softegg/Stylish-Trucker-Belt-Synthesizer/photos/Back of v4 plastic enclosure.JPG

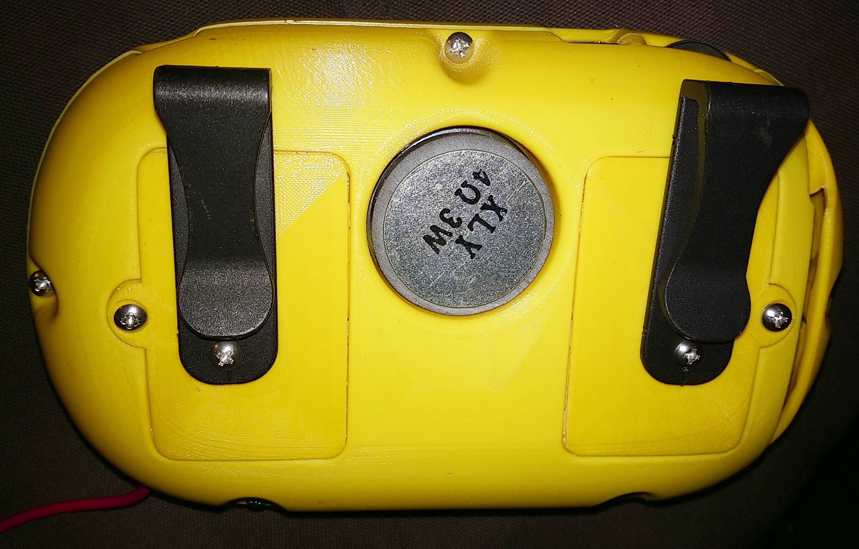
photos/Back of v4 plastic enclosure.JPG
