softegg/Stylish-Trucker-Belt-Synthesizer/photos/PCBs from Ai Green 2.jpg

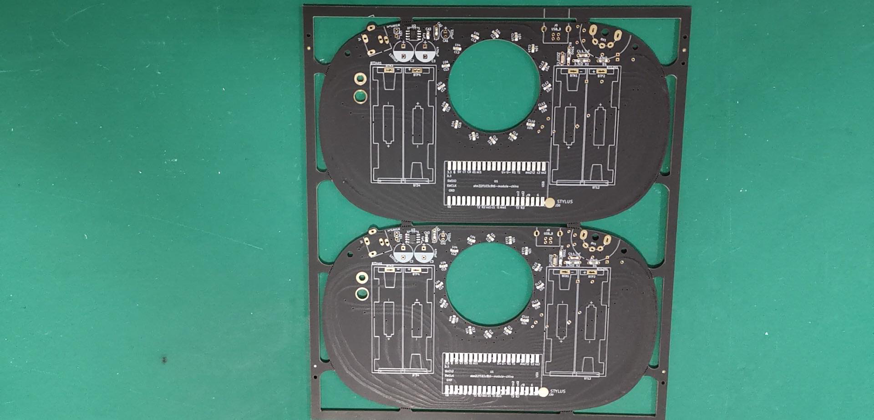
photos/PCBs from Ai Green 2.jpg
