softegg/Stylish-Trucker-Belt-Synthesizer/renders etc/board back only.png

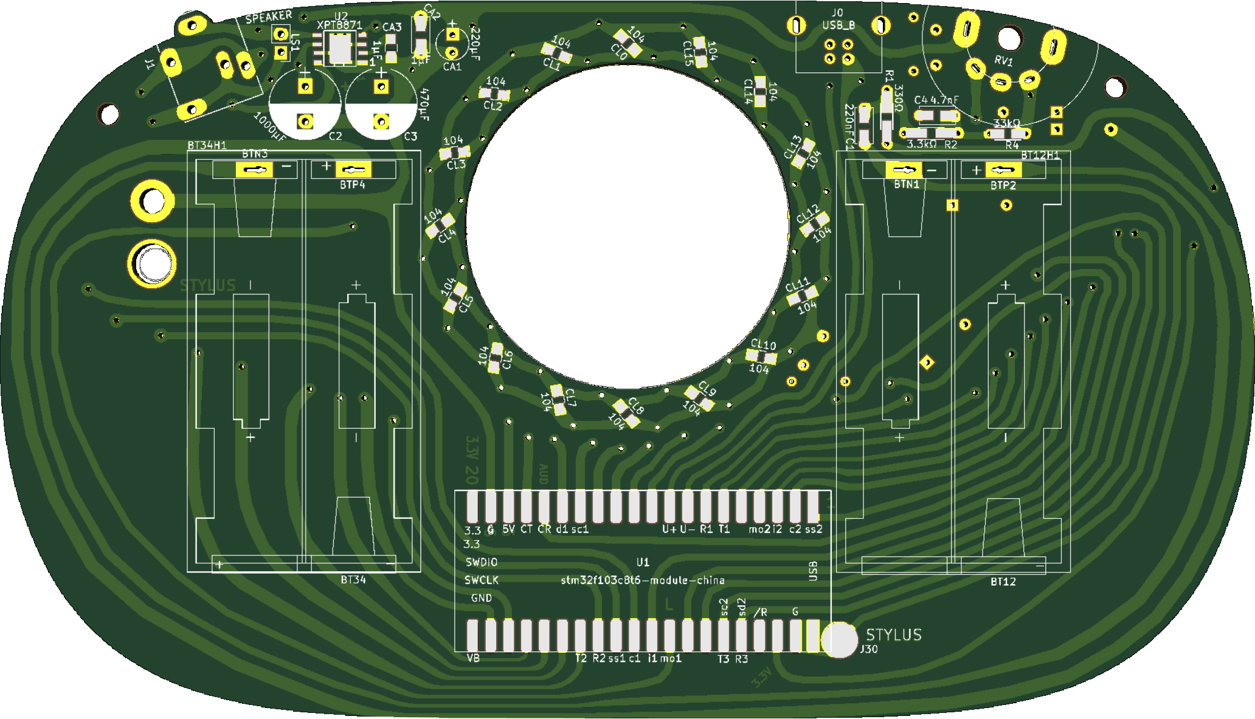
renders etc/board back only.png
