softegg/Stylish-Trucker-Belt-Synthesizer/renders etc/board front only.png

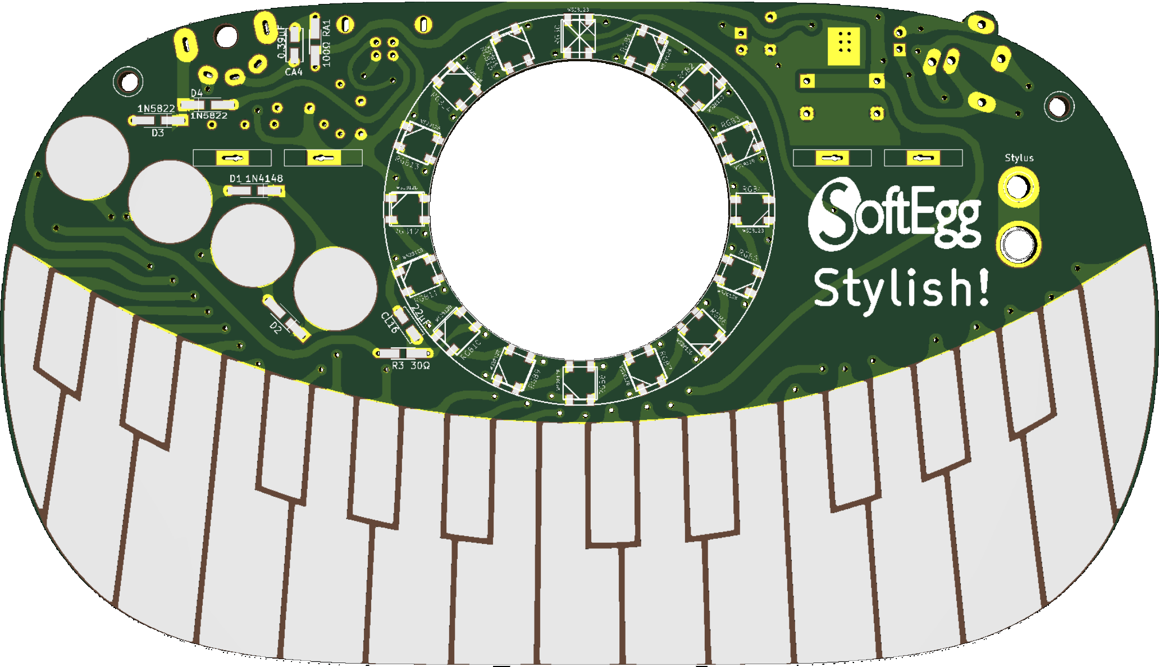
renders etc/board front only.png
