softegg/Stylish-Trucker-Belt-Synthesizer/renders etc/Stylish PCB V4.PNG

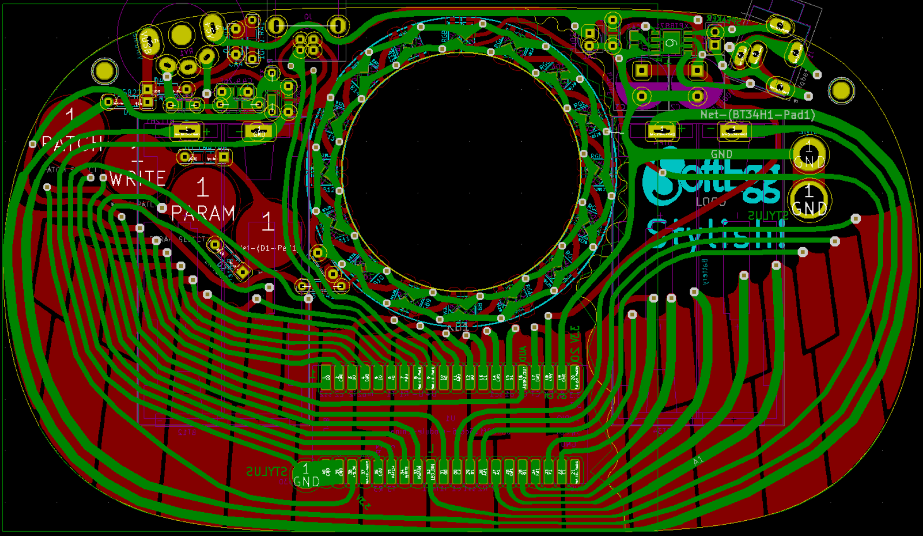
renders etc/Stylish PCB V4.PNG
