softegg/Stylish-Trucker-Belt-Synthesizer/3d models/Normal Models/STEP/Stylish Belt Synth V4 LED Bezel.step

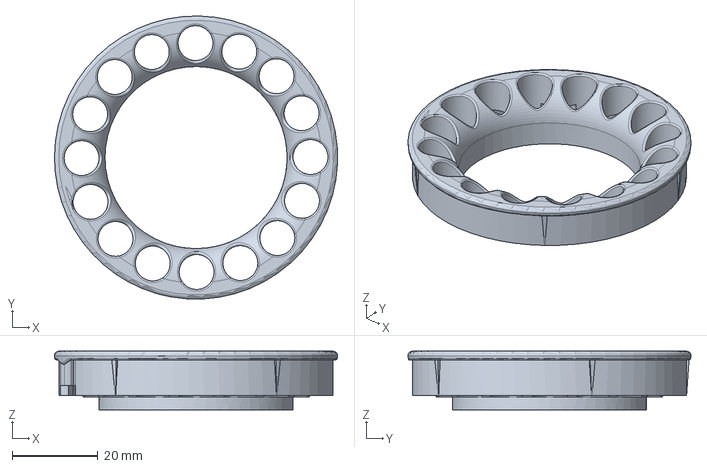
[picture p25: CAD file, 2019-10-15]
3d models/Normal Models/STEP/Stylish Belt Synth V4 LED Bezel.step
65.8 x 65.8 x 13.6 mm
