softegg/Stylish-Trucker-Belt-Synthesizer/3d models/Stylish Belt Synth V2 Left Battery Door.step

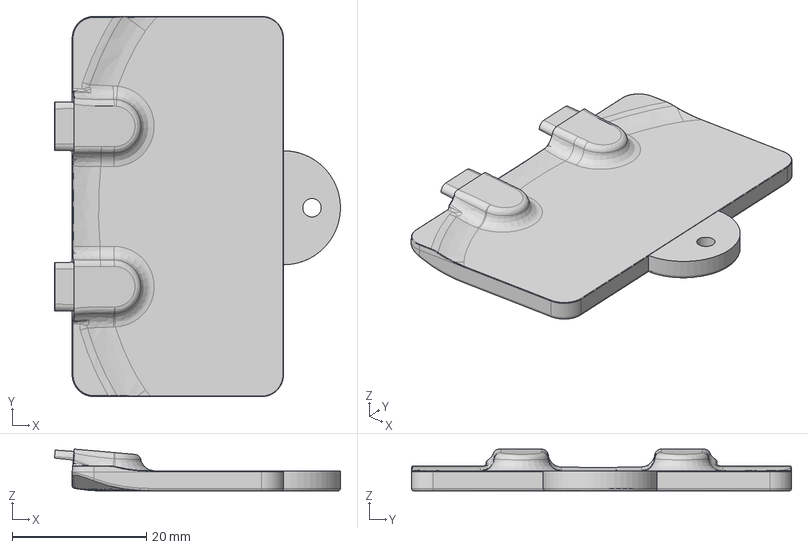
[picture p26: CAD file, 2019-07-12]
3d models/Stylish Belt Synth V2 Left Battery Door.step
42.6 x 56.7 x 6.25 mm
