softegg/Stylish-Trucker-Belt-Synthesizer/3d models/woodCNC/StylishWoodFrontFixtureCNC.stl

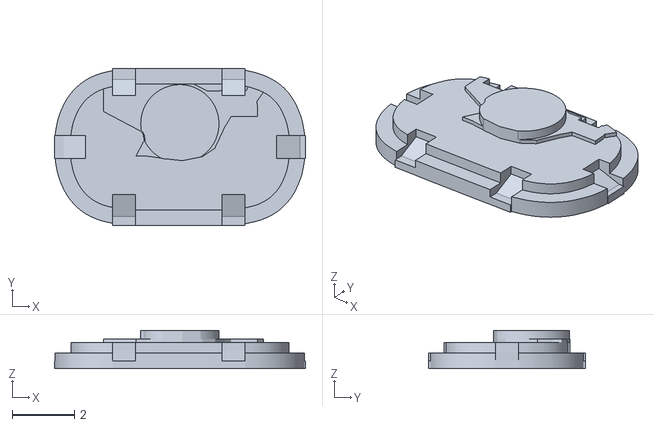
[picture p27: CAD file, 2019-08-12]
3d models/woodCNC/StylishWoodFrontFixtureCNC.stl
8.06 x 5.06 x 1.22
