softegg/Stylish-Trucker-Belt-Synthesizer/3d models/Mold/Negative/STEP/Stylish Belt Synth - Top - Outside Negative.step

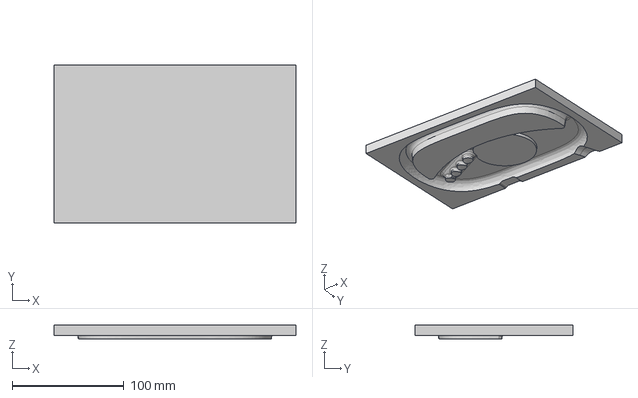
[picture p28: CAD file, 2020-02-13]
3d models/Mold/Negative/STEP/Stylish Belt Synth - Top - Outside Negative.step
216.3 x 141.5 x 12.6 mm
