softegg/Stylish-Trucker-Belt-Synthesizer/3d models/Mold/Positive - Mold Molds/STEP/Stylish Belt Synth - LED Lightpipe- Inside Positive.step

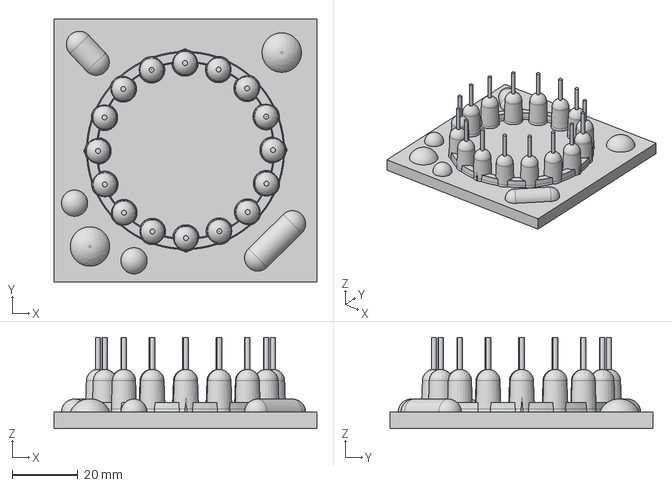
[picture p29: CAD file, 2020-03-12]
3d models/Mold/Positive - Mold Molds/STEP/Stylish Belt Synth - LED Lightpipe- Inside Positive.step
80.0 x 80.0 x 27.8 mm
LED Bezel
LED Lightpipe
