softegg/Stylish-Trucker-Belt-Synthesizer/3d models/Stylish Belt Synth V2 Switch Toggle.step

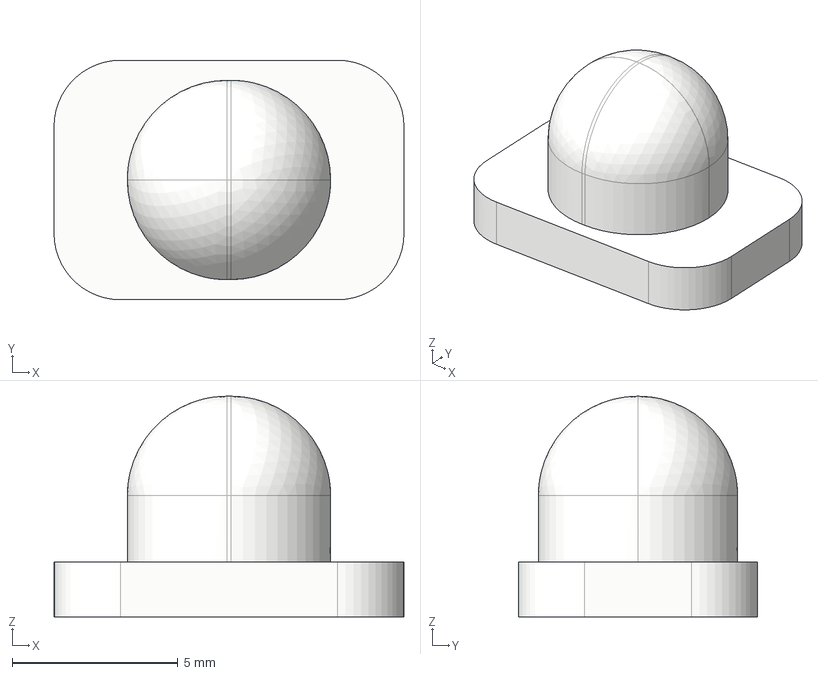
[picture p30: CAD file, 2019-07-12]
3d models/Stylish Belt Synth V2 Switch Toggle.step
10.5 x 7.22 x 6.65 mm
