softegg/Stylish-Trucker-Belt-Synthesizer/3d models/woodCNC/StylishWoodBackFixtureCNC.stl

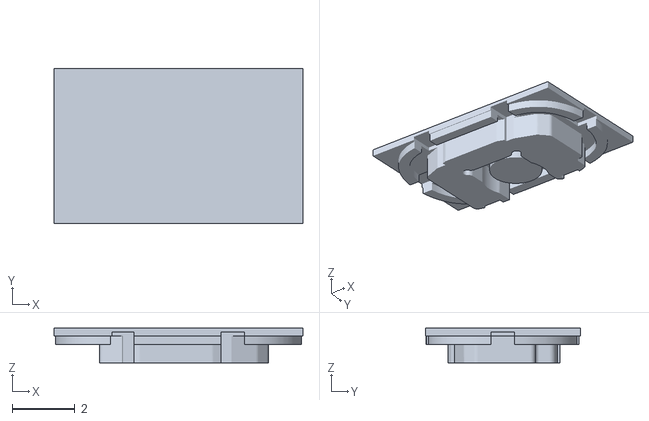
[picture p31: CAD file, 2019-08-12]
3d models/woodCNC/StylishWoodBackFixtureCNC.stl
7.92 x 4.94 x 1.11
