softegg/Stylish-Trucker-Belt-Synthesizer/3d models/Mold/Positive - Mold Molds/STEP/Stylish Belt Synth - LED Bezel - Outside Positive.step

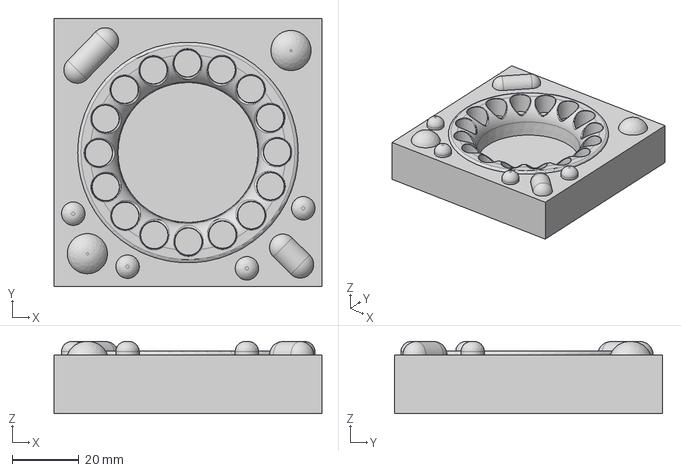
[picture p33: CAD file, 2020-03-12]
3d models/Mold/Positive - Mold Molds/STEP/Stylish Belt Synth - LED Bezel - Outside Positive.step
80.0 x 80.0 x 21.5 mm
