softegg/Stylish-Trucker-Belt-Synthesizer/3d models/Stylish Belt Synth V2 Bezel.stl

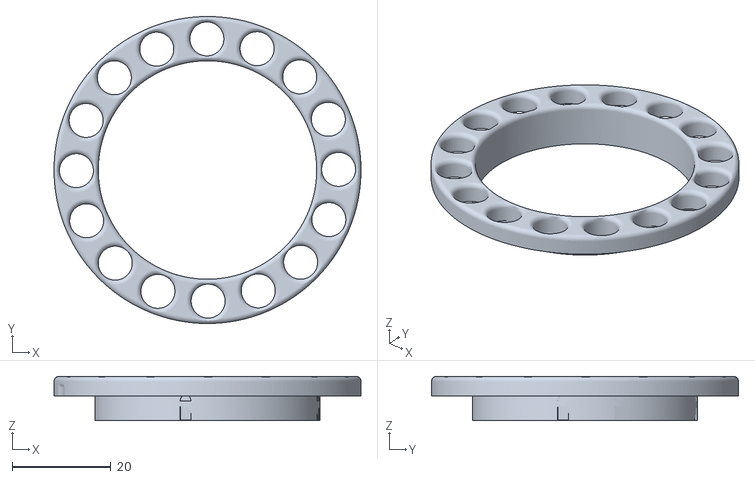
[picture p34: CAD file, 2019-06-09]
3d models/Stylish Belt Synth V2 Bezel.stl
62.3 x 62.3 x 9.00
