softegg/Stylish-Trucker-Belt-Synthesizer/3d models/woodCNC/StylishWoodFrontCNC.stl

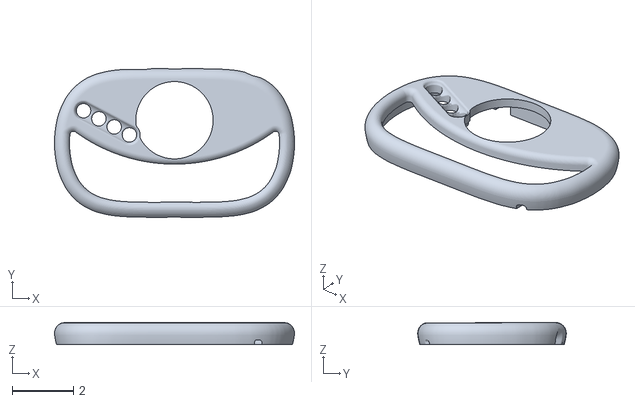
[picture p35: CAD file, 2019-08-07]
3d models/woodCNC/StylishWoodFrontCNC.stl
7.87 x 4.87 x 0.726
