softegg/Stylish-Trucker-Belt-Synthesizer/3d models/Mold/Negative/STEP/Stylish Belt Synth - Battery Door 2 - Inside Negative.step

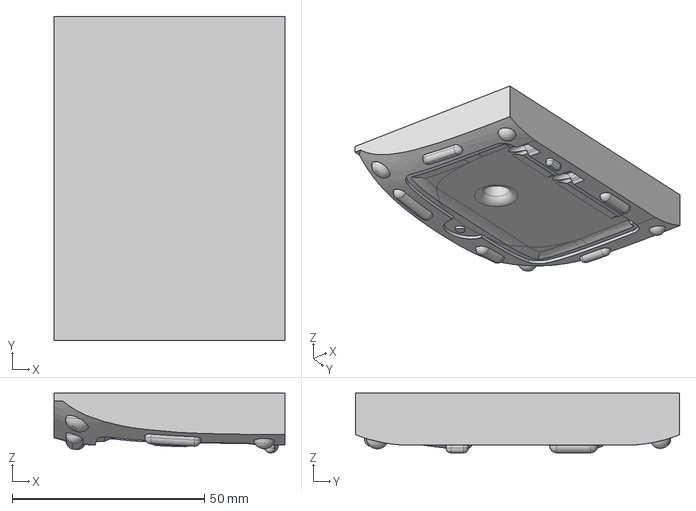
[picture p36: CAD file, 2020-01-29]
3d models/Mold/Negative/STEP/Stylish Belt Synth - Battery Door 2 - Inside Negative.step
60.0 x 84.3 x 15.5 mm
