softegg/Stylish-Trucker-Belt-Synthesizer/3d models/Belt Clip.stl

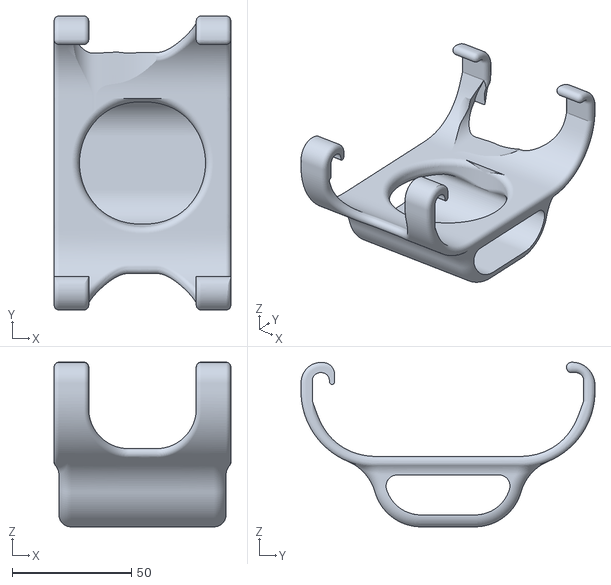
[picture p37: CAD file, 2018-11-03]
3d models/Belt Clip.stl
74.0 x 123.1 x 68.9
