softegg/Stylish-Trucker-Belt-Synthesizer/3d models/Mold/Negative/STEP/Stylish Belt Synth - Battery Door 1 - Outside Negative.step

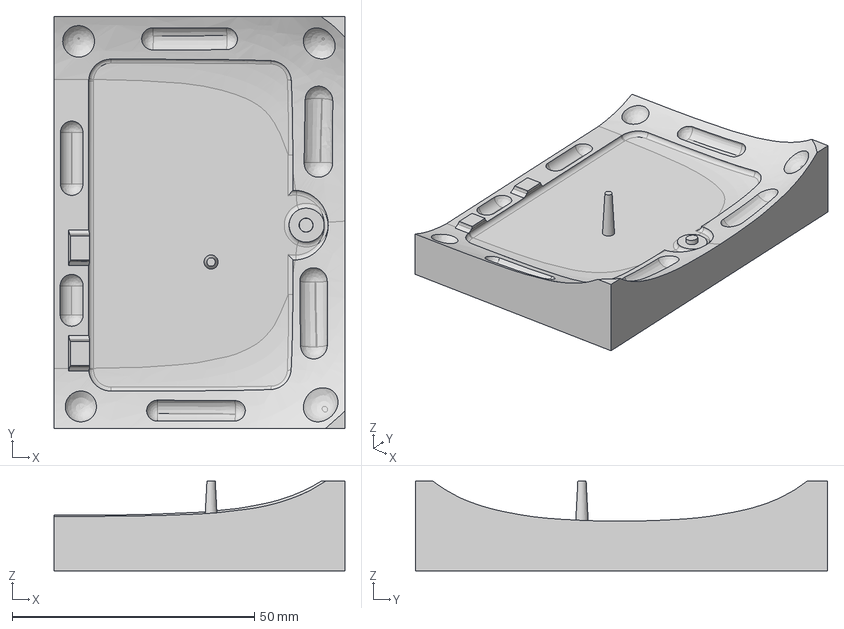
[picture p38: CAD file, 2020-01-29]
3d models/Mold/Negative/STEP/Stylish Belt Synth - Battery Door 1 - Outside Negative.step
60.0 x 85.0 x 18.5 mm
