softegg/Stylish-Trucker-Belt-Synthesizer/3d models/Mold/Positive - Mold Molds/STEP/Stylish Belt Synth - Battery Door 1 - Inside Positive.step

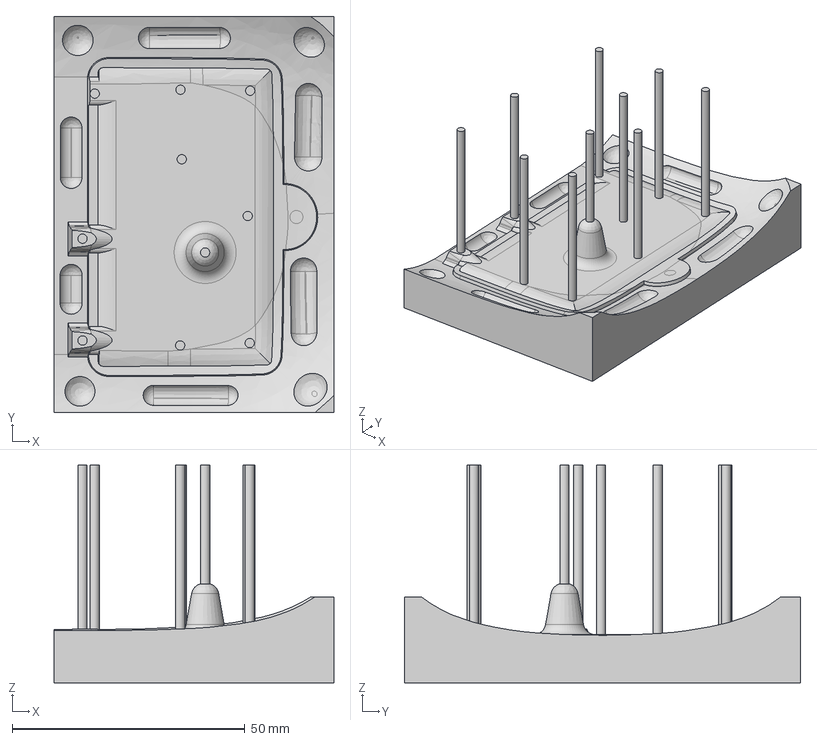
[picture p39: CAD file, 2020-01-29]
3d models/Mold/Positive - Mold Molds/STEP/Stylish Belt Synth - Battery Door 1 - Inside Positive.step
60.0 x 85.0 x 46.8 mm
