softegg/Stylish-Trucker-Belt-Synthesizer/3d models/woodCNC/Stylish Belt Synth CNC Wood Top Interior.dxf

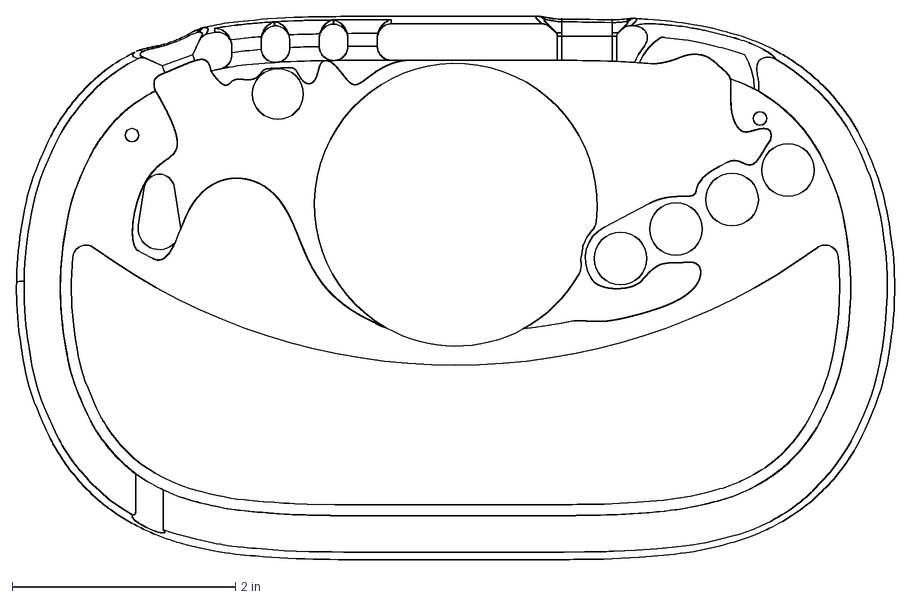
[picture p40: CAD file, 2019-08-07]
3d models/woodCNC/Stylish Belt Synth CNC Wood Top Interior.dxf
7.87 x 4.87 in
