softegg/Stylish-Trucker-Belt-Synthesizer/3d models/LED Bezel Outer Black TPE.stl

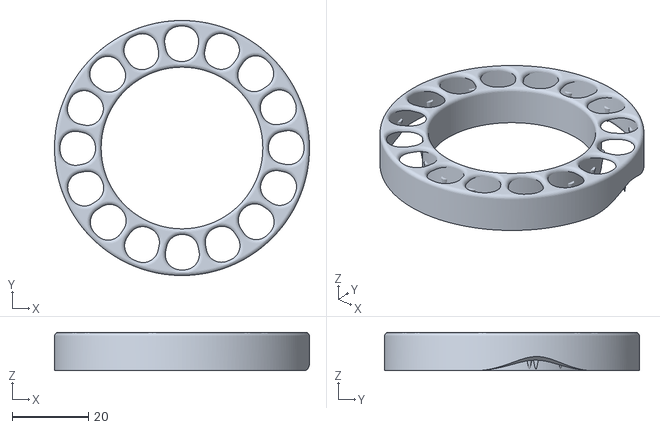
[picture p41: CAD file, 2018-11-03]
3d models/LED Bezel Outer Black TPE.stl
66.8 x 66.8 x 10.1
