softegg/Stylish-Trucker-Belt-Synthesizer/3d models/Mold/Negative/STEP/Stylish Belt Synth - Battery Door 2 - Outside Negative.step

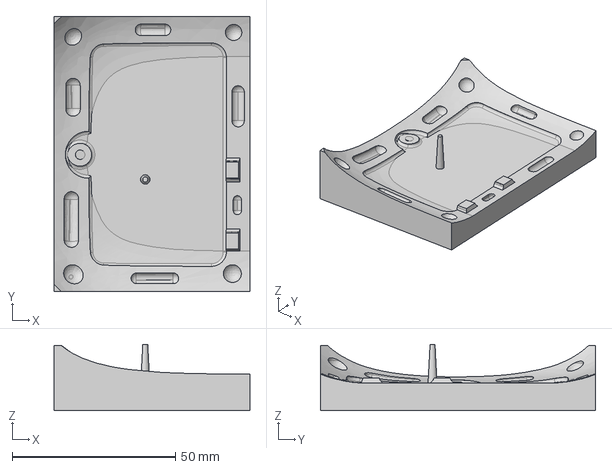
[picture p42: CAD file, 2020-01-29]
3d models/Mold/Negative/STEP/Stylish Belt Synth - Battery Door 2 - Outside Negative.step
60.0 x 84.3 x 20.4 mm
