softegg/Stylish-Trucker-Belt-Synthesizer/3d models/woodCNC/Stylish Belt Synth CNC Wood Bottom Interior.dxf

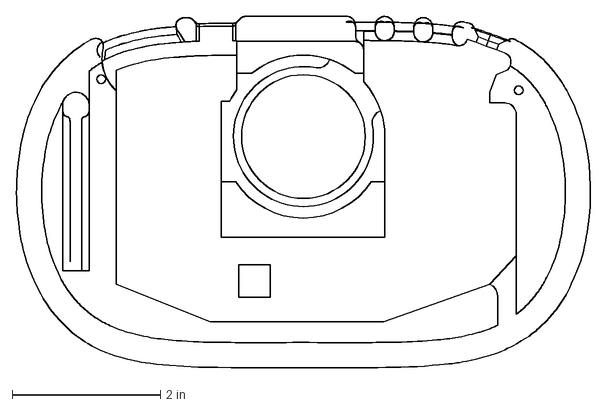
[picture p43: CAD file, 2019-08-04]
3d models/woodCNC/Stylish Belt Synth CNC Wood Bottom Interior.dxf
7.74 x 4.73 in
