softegg/Stylish-Trucker-Belt-Synthesizer/3d models/Amp Cover.stl

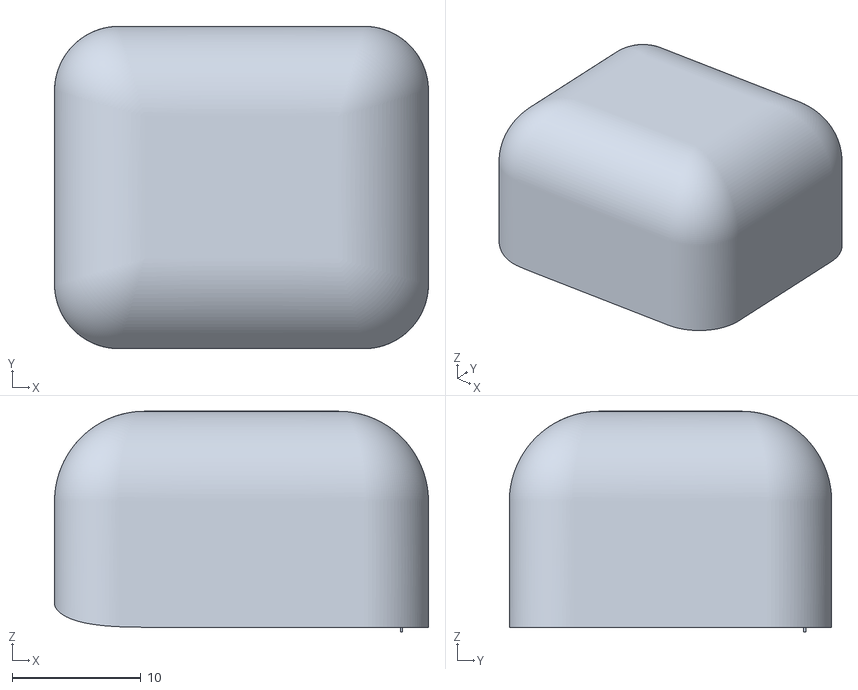
[picture p44: CAD file, 2018-11-03]
3d models/Amp Cover.stl
29.0 x 25.0 x 17.1
