softegg/Stylish-Trucker-Belt-Synthesizer/3d models/Mold/Negative/STEP/Stylish Belt Synth - Bottom - Outside Negative.step

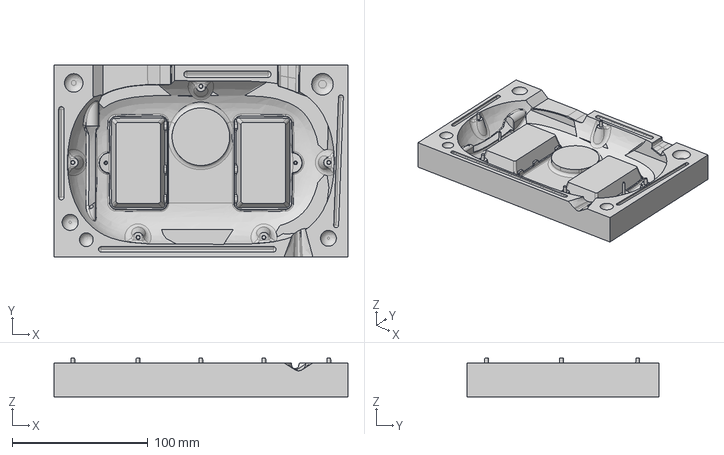
[picture p45: CAD file, 2020-01-27]
3d models/Mold/Negative/STEP/Stylish Belt Synth - Bottom - Outside Negative.step
216.3 x 141.5 x 28.5 mm
Top top
Bottom Molds
