softegg/Stylish-Trucker-Belt-Synthesizer/3d models/Mold/Positive - Mold Molds/STEP/Stylish Belt Synth - Battery Door 2 - Inside Positive.step

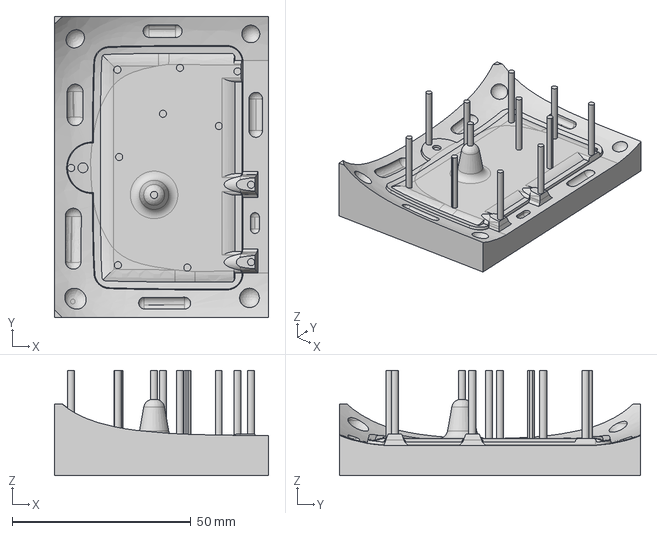
[picture p46: CAD file, 2020-01-29]
3d models/Mold/Positive - Mold Molds/STEP/Stylish Belt Synth - Battery Door 2 - Inside Positive.step
60.0 x 84.3 x 29.4 mm
