softegg/Stylish-Trucker-Belt-Synthesizer/3d models/woodCNC/Stylish Belt Synth CNC Wood Top Fixturing Jig.dxf

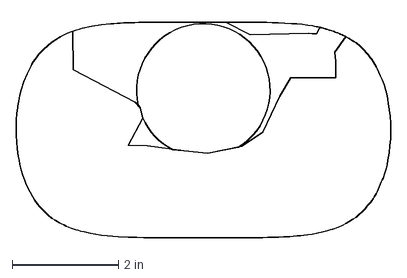
[picture p47: CAD file, 2019-08-01]
3d models/woodCNC/Stylish Belt Synth CNC Wood Top Fixturing Jig.dxf
7.06 x 4.18 in
