softegg/Stylish-Trucker-Belt-Synthesizer/3d models/Front v2.stl

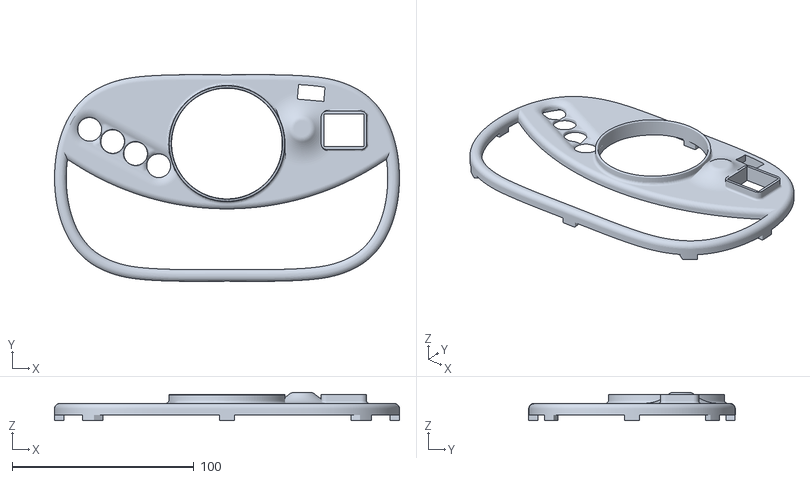
[picture p48: CAD file, 2018-11-03]
3d models/Front v2.stl
189.8 x 113.7 x 15.5
