softegg/Stylish-Trucker-Belt-Synthesizer/3d models/Mold/Positive - Mold Molds/STEP/Stylish Belt Synth - Bottom - Outside Positive.step

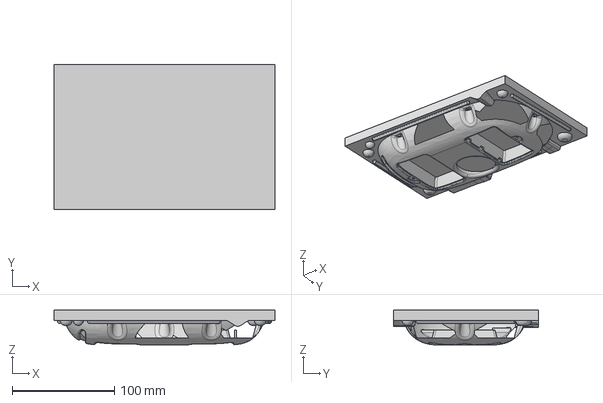
[picture p49: CAD file, 2020-01-27]
3d models/Mold/Positive - Mold Molds/STEP/Stylish Belt Synth - Bottom - Outside Positive.step
216.3 x 141.5 x 34.0 mm
Top top
Bottom Molds
