softegg/Stylish-Trucker-Belt-Synthesizer/3d models/woodCNC/Stylish Belt Synth CNC Wood Bottom Fixturing Jig.dxf

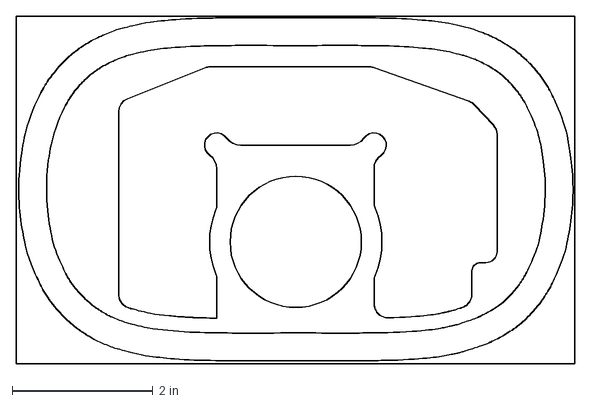
[picture p50: CAD file, 2019-07-18]
3d models/woodCNC/Stylish Belt Synth CNC Wood Bottom Fixturing Jig.dxf
7.92 x 4.94 in
