softegg/Stylish-Trucker-Belt-Synthesizer/3d models/LED Bezel Inner Translucent PLA.stl

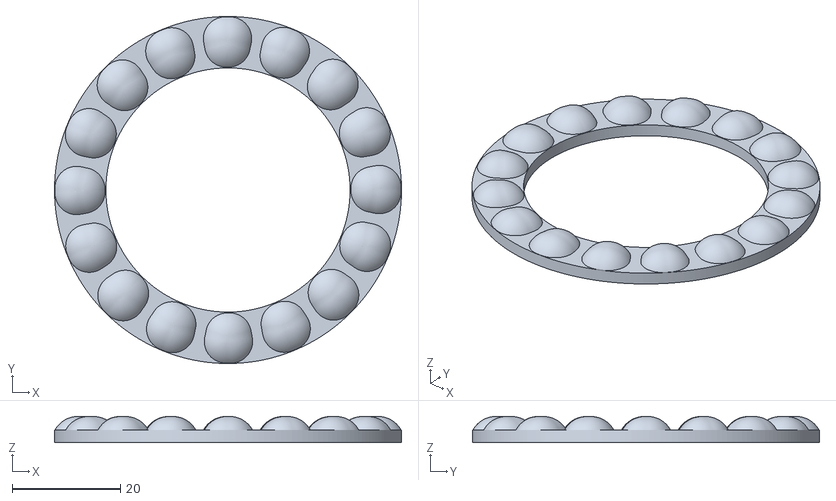
[picture p51: CAD file, 2018-11-03]
3d models/LED Bezel Inner Translucent PLA.stl
64.0 x 64.0 x 4.80
