softegg/Stylish-Trucker-Belt-Synthesizer/3d models/woodCNC/Stylish Belt Synth V4 Wood CNC Top.step

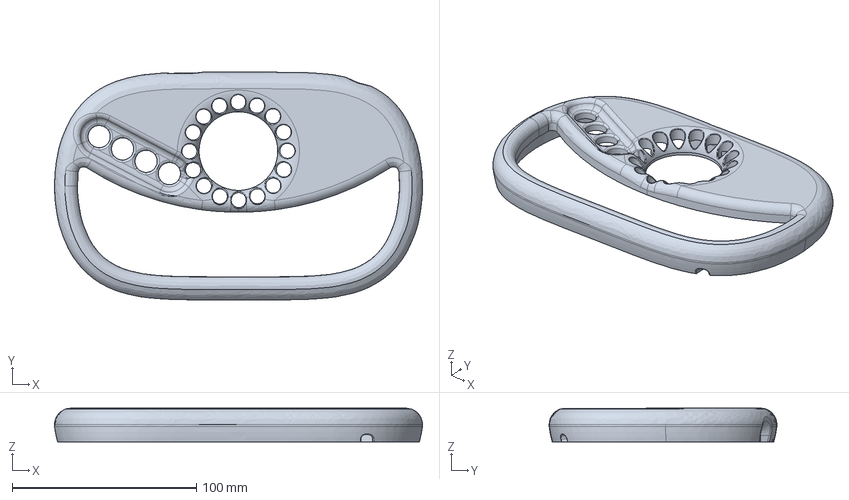
[picture p52: CAD file, 2019-07-16]
3d models/woodCNC/Stylish Belt Synth V4 Wood CNC Top.step
199.8 x 123.7 x 18.4 mm
