softegg/Stylish-Trucker-Belt-Synthesizer/3d models/Switch.stl

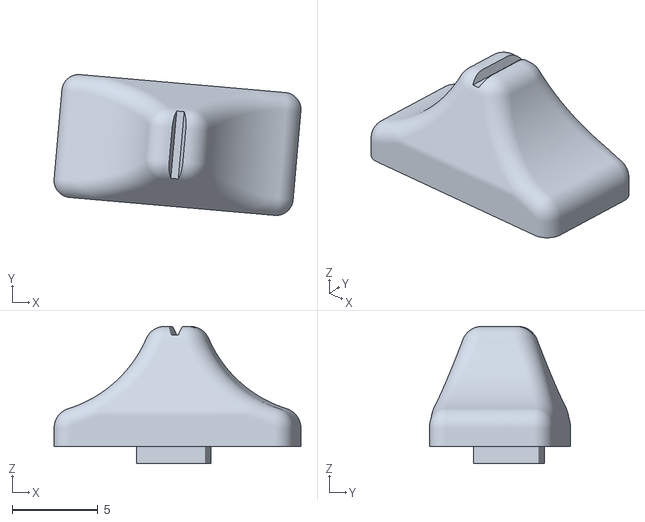
[picture p53: CAD file, 2018-11-03]
3d models/Switch.stl
14.4 x 8.21 x 8.00
