softegg/Stylish-Trucker-Belt-Synthesizer/3d models/woodCNC/Stylish Belt Synth V4 Wood CNC Bottom.step

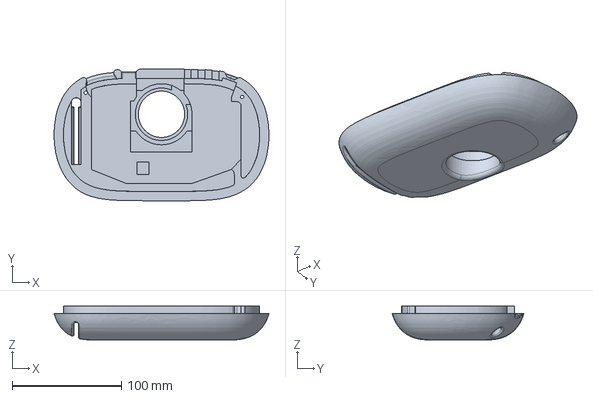
[picture p54: CAD file, 2019-07-16]
3d models/woodCNC/Stylish Belt Synth V4 Wood CNC Bottom.step
196.4 x 120.2 x 30.8 mm
