softegg/Stylish-Trucker-Belt-Synthesizer/3d models/Switch Plug.stl

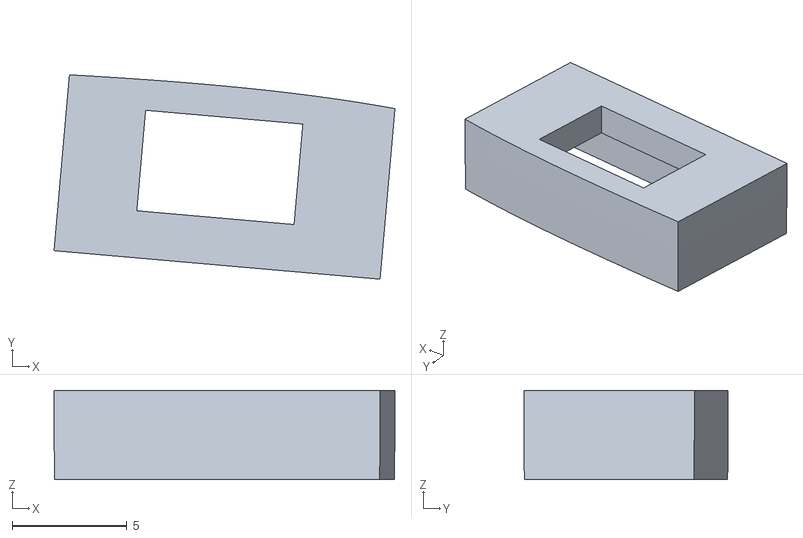
[picture p55: CAD file, 2018-11-03]
3d models/Switch Plug.stl
14.9 x 8.92 x 3.90
