softegg/Stylish-Trucker-Belt-Synthesizer/3d models/woodCNC/Stylish Belt Synth V4 Wood CNC Back Fixturing Jig.step

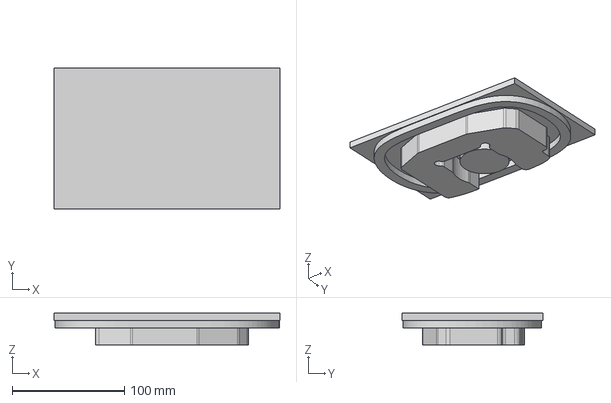
[picture p56: CAD file, 2019-07-16]
3d models/woodCNC/Stylish Belt Synth V4 Wood CNC Back Fixturing Jig.step
201.2 x 125.4 x 28.2 mm
