softegg/Stylish-Trucker-Belt-Synthesizer/3d models/SpeakerHolder.stl

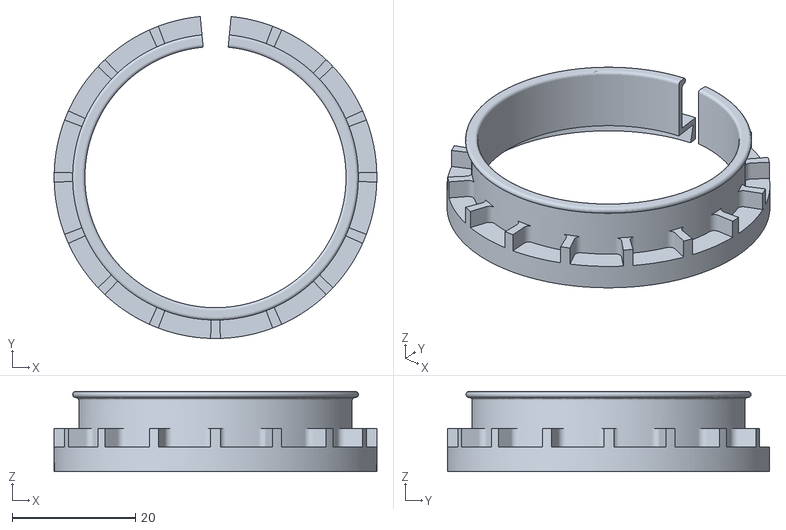
[picture p57: CAD file, 2018-10-17]
3d models/SpeakerHolder.stl
52.3 x 52.2 x 13.0
