softegg/Stylish-Trucker-Belt-Synthesizer/3d models/woodCNC/Stylish Belt Synth V4 Wood CNC Top Fixturing Jig.step

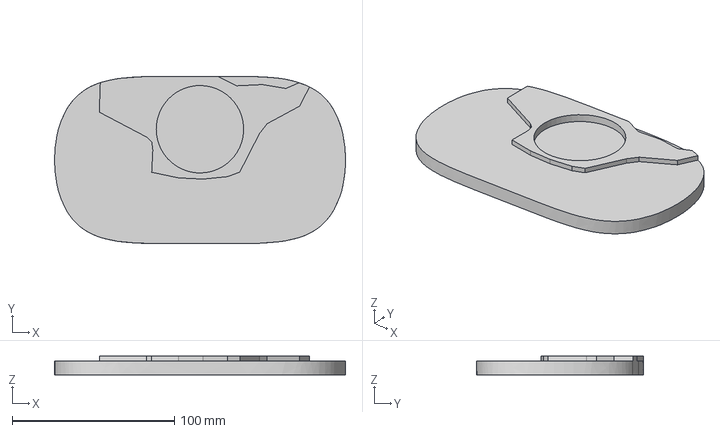
[picture p58: CAD file, 2019-07-16]
3d models/woodCNC/Stylish Belt Synth V4 Wood CNC Top Fixturing Jig.step
179.2 x 103.1 x 11.4 mm
