softegg/Stylish-Trucker-Belt-Synthesizer/3d models/woodCNC/Stylish Belt Synth V4 Wood CNC Top Inner.step

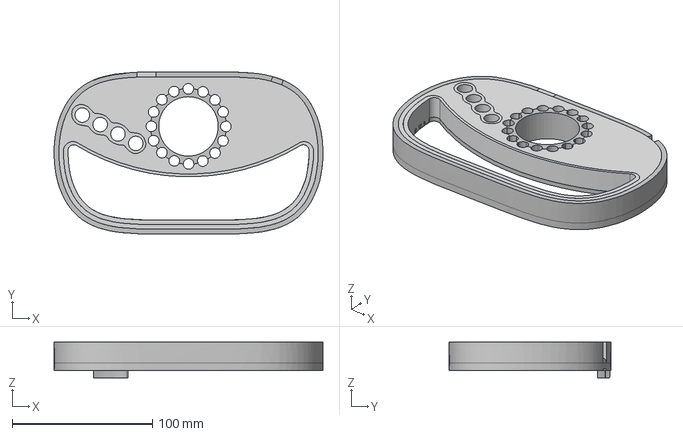
[picture p59: CAD file, 2019-07-12]
3d models/woodCNC/Stylish Belt Synth V4 Wood CNC Top Inner.step
191.8 x 115.7 x 25.4 mm
