softegg/Stylish-Trucker-Belt-Synthesizer/3d models/Back.stl

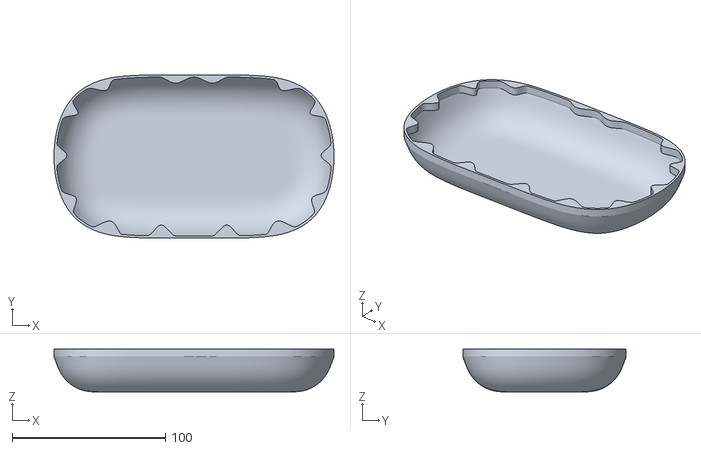
[picture p60: CAD file, 2018-10-07]
3d models/Back.stl
182.8 x 106.7 x 28.0
