softegg/Stylish-Trucker-Belt-Synthesizer/3d models/woodCNC/StylishWoodBackCNC.stl

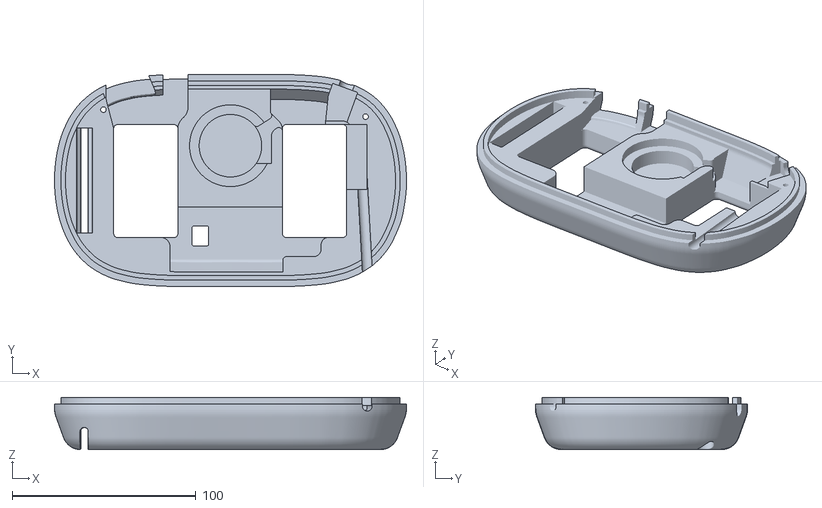
[picture p61: CAD file, 2019-07-08]
3d models/woodCNC/StylishWoodBackCNC.stl
191.8 x 115.7 x 28.5
