softegg/Stylish-Trucker-Belt-Synthesizer/photos/Plastic Assembled.JPG

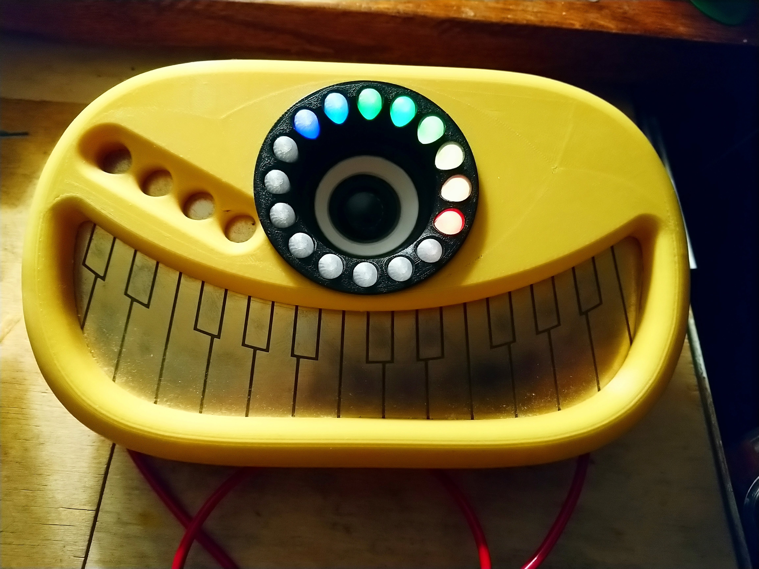
photos/Plastic Assembled.JPG
