softegg/Stylish-Trucker-Belt-Synthesizer/photos/Stylish Assembled Full 1.JPG

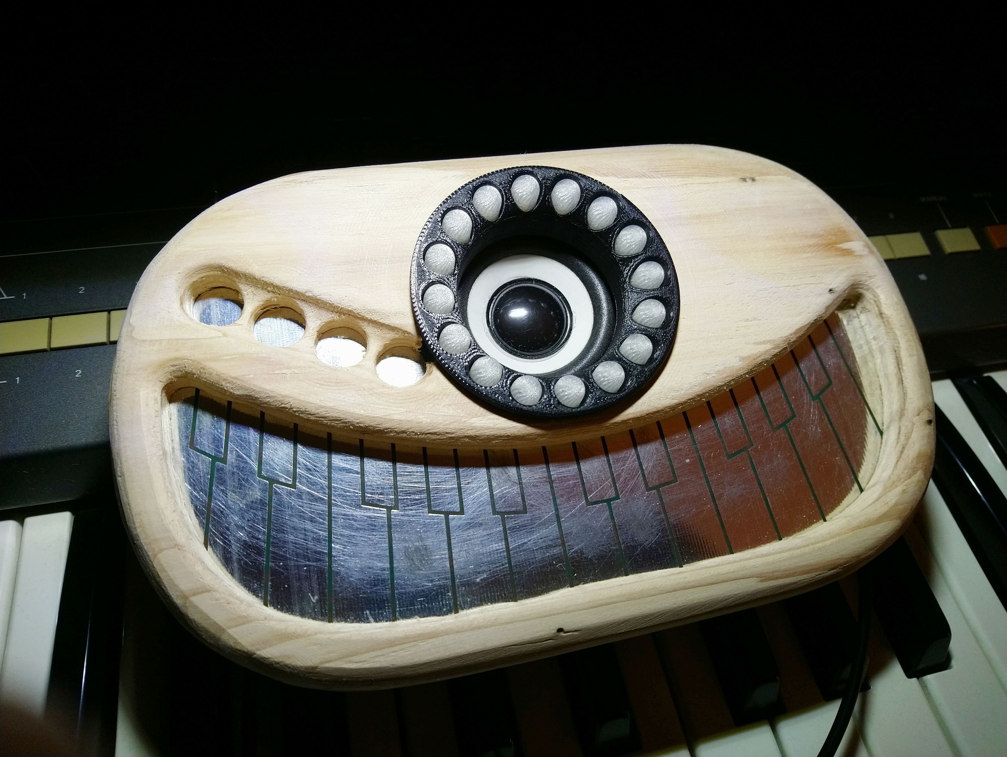
photos/Stylish Assembled Full 1.JPG
