softegg/Stylish-Trucker-Belt-Synthesizer/photos/Stylish V4 PCB Assembled  Back.jpg

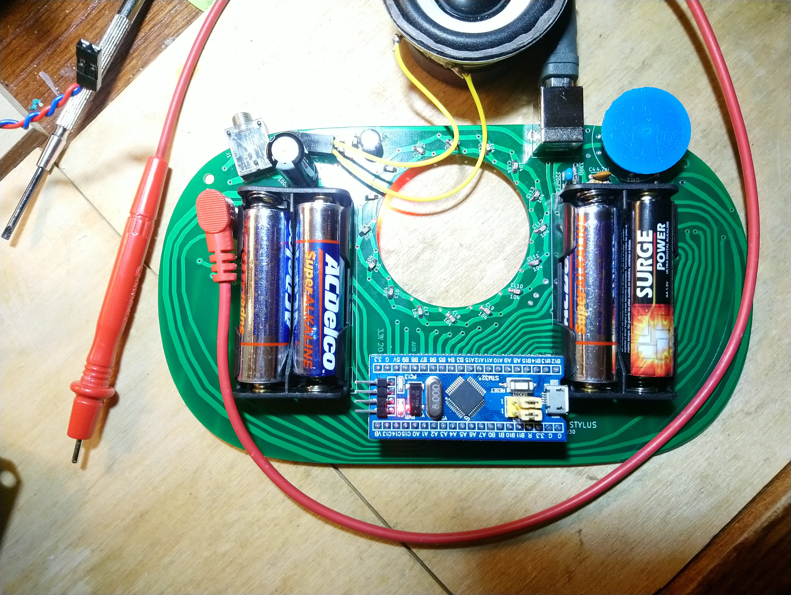
photos/Stylish V4 PCB Assembled Back.jpg
