softegg/Stylish-Trucker-Belt-Synthesizer/photos/Stylish V4 PCB Assembled  LED ring RC detail.jpg

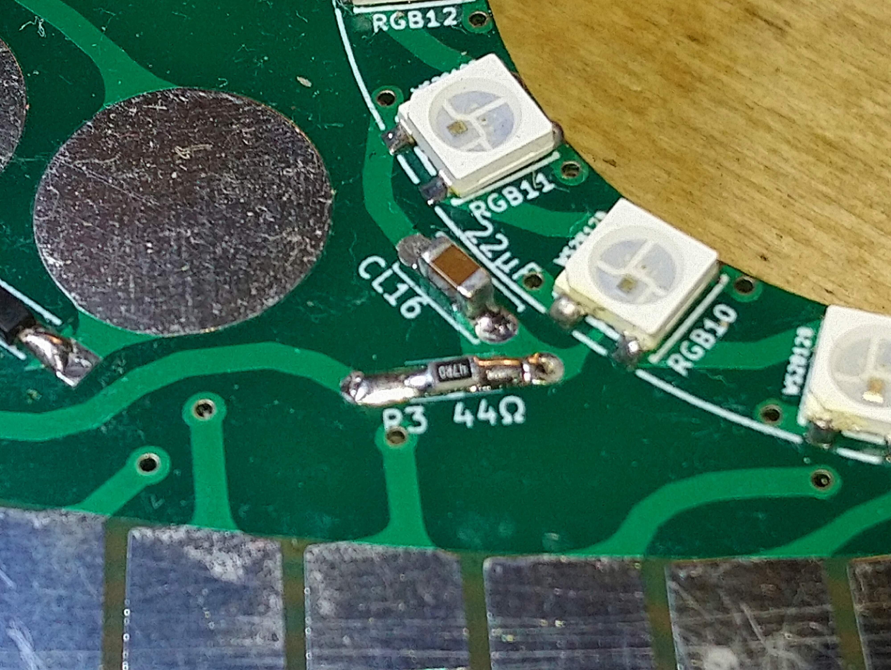
photos/Stylish V4 PCB Assembled LED ring RC detail.jpg
