softegg/Stylish-Trucker-Belt-Synthesizer/photos/Stylish V4 PCB Assembled Amplifier detail back.jpg

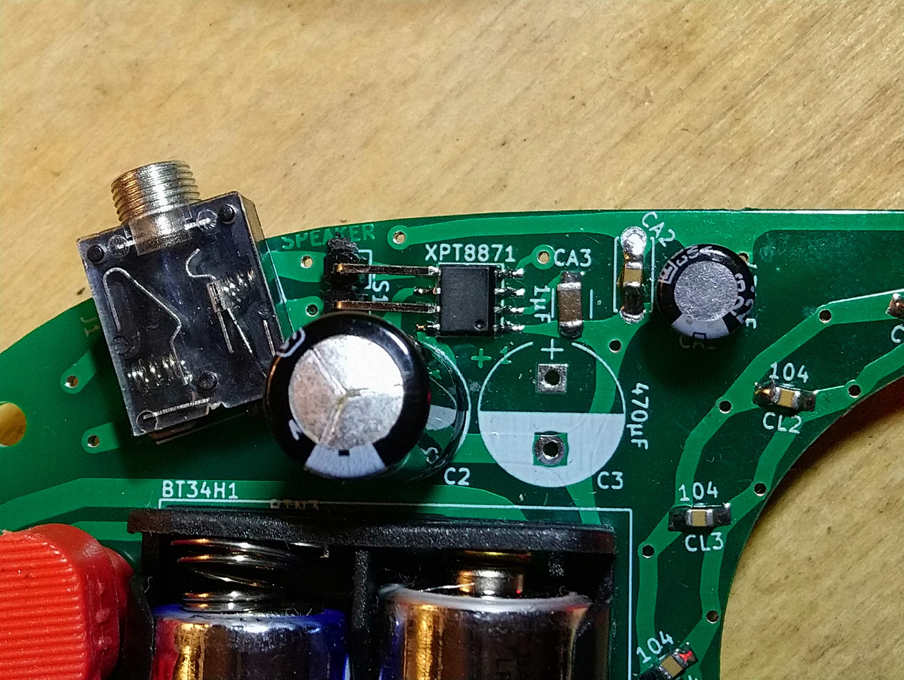
photos/Stylish V4 PCB Assembled Amplifier detail back.jpg
