softegg/Stylish-Trucker-Belt-Synthesizer/photos/Stylish V4 PCB Assembled Front .jpg

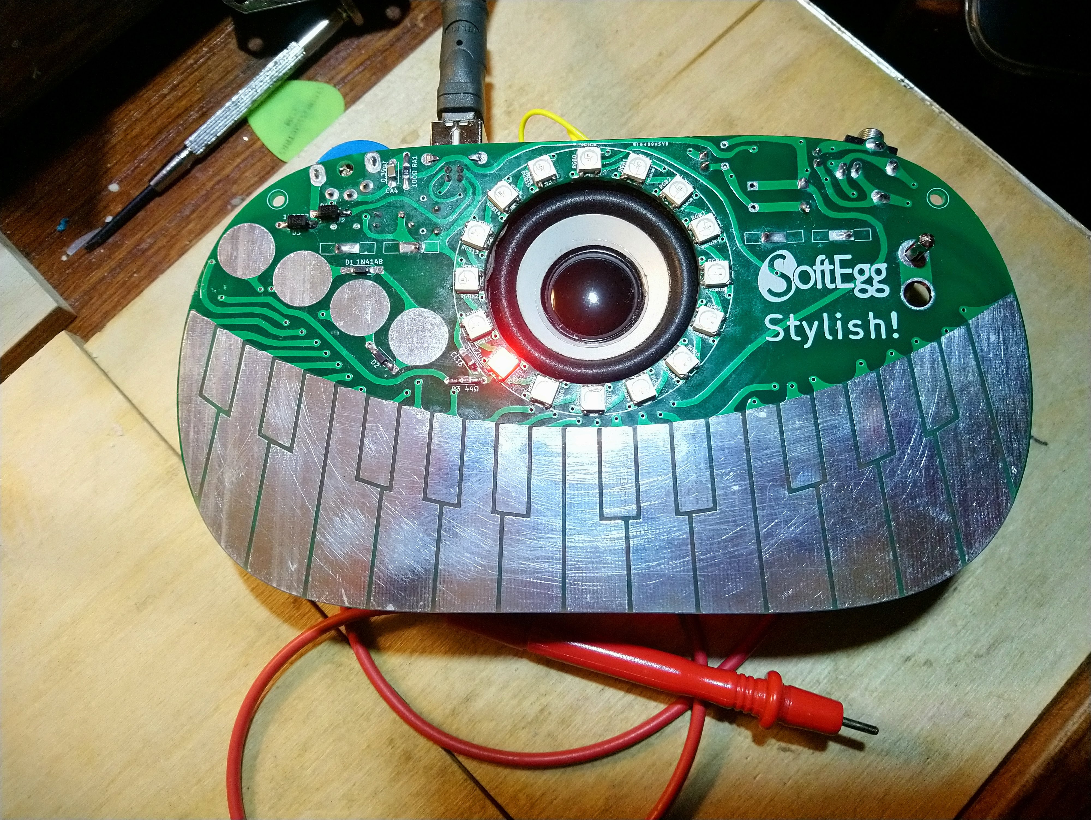
photos/Stylish V4 PCB Assembled Front .jpg
