softegg/Stylish-Trucker-Belt-Synthesizer/photos/Stylish V4 PCB Assembled Select diodes detail front.jpg

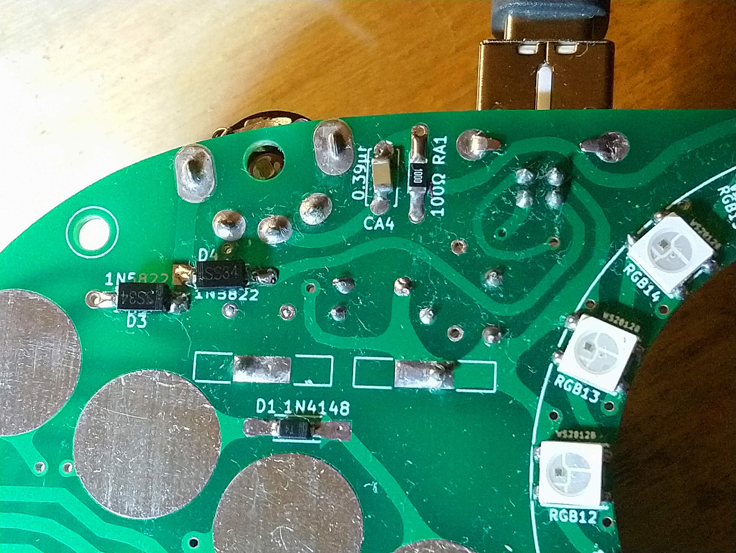
photos/Stylish V4 PCB Assembled Select diodes detail front.jpg
