softegg/Stylish-Trucker-Belt-Synthesizer/photos/Stylish V4 PCB Assembled STM32 female pinheader detail back.jpg

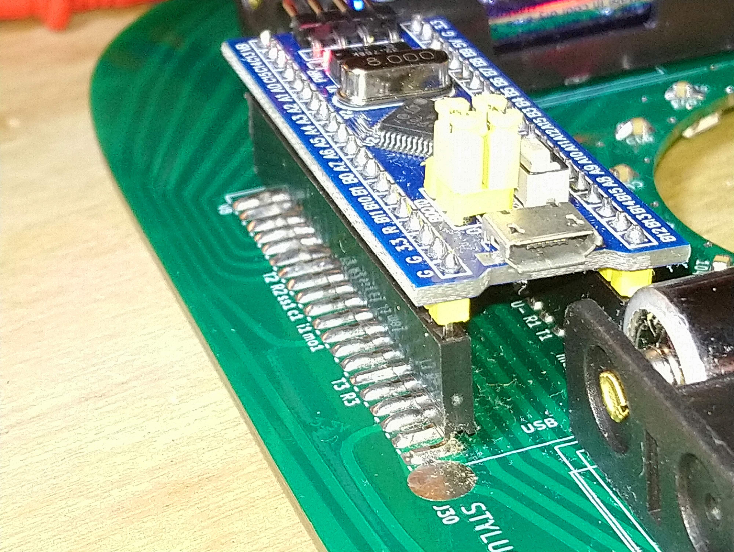
photos/Stylish V4 PCB Assembled STM32 female pinheader detail back.jpg
