softegg/Stylish-Trucker-Belt-Synthesizer/3d models/woodCNC/Stylish Belt Synth V4 CNC Wood Enclosure Bottom Inside Drawing.pdf

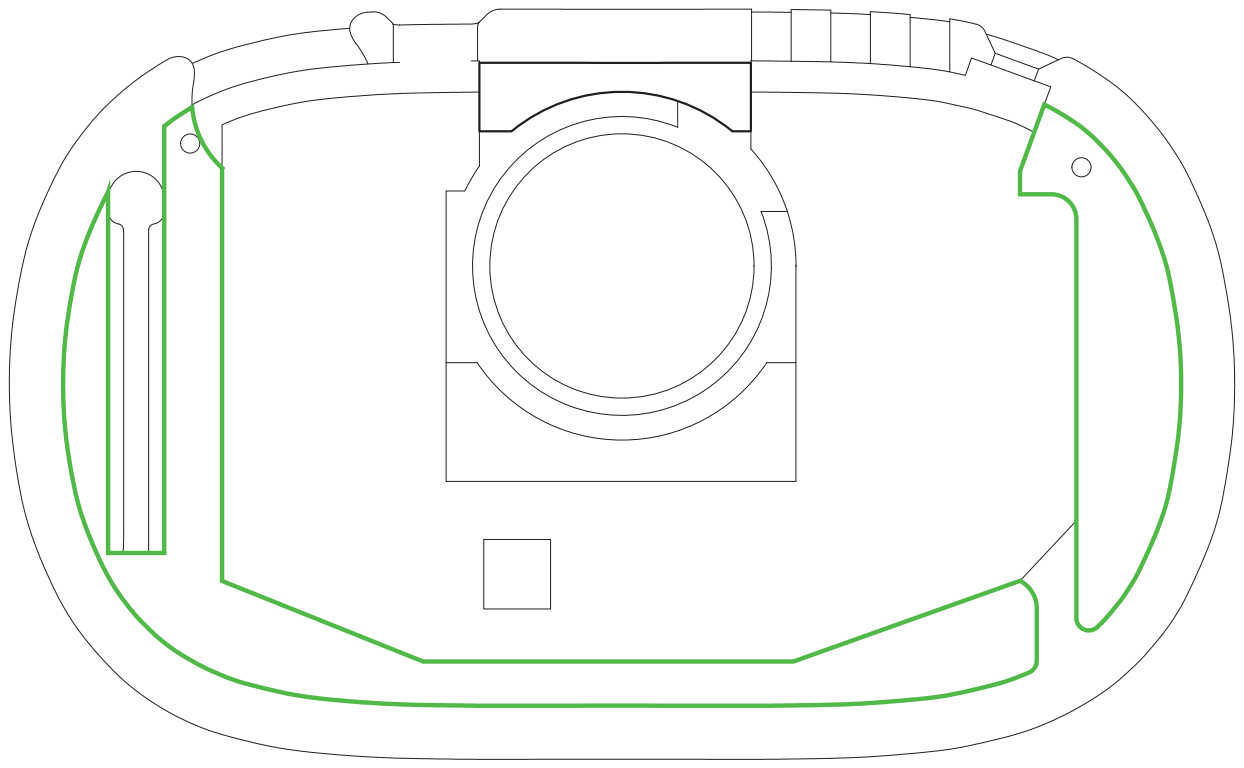
[picture p84: page 1]
