softegg/Stylish-Trucker-Belt-Synthesizer/3d models/woodCNC/Stylish Belt Synth V4 Front Inner CNC Wood Enclosure Drawing v2.pdf

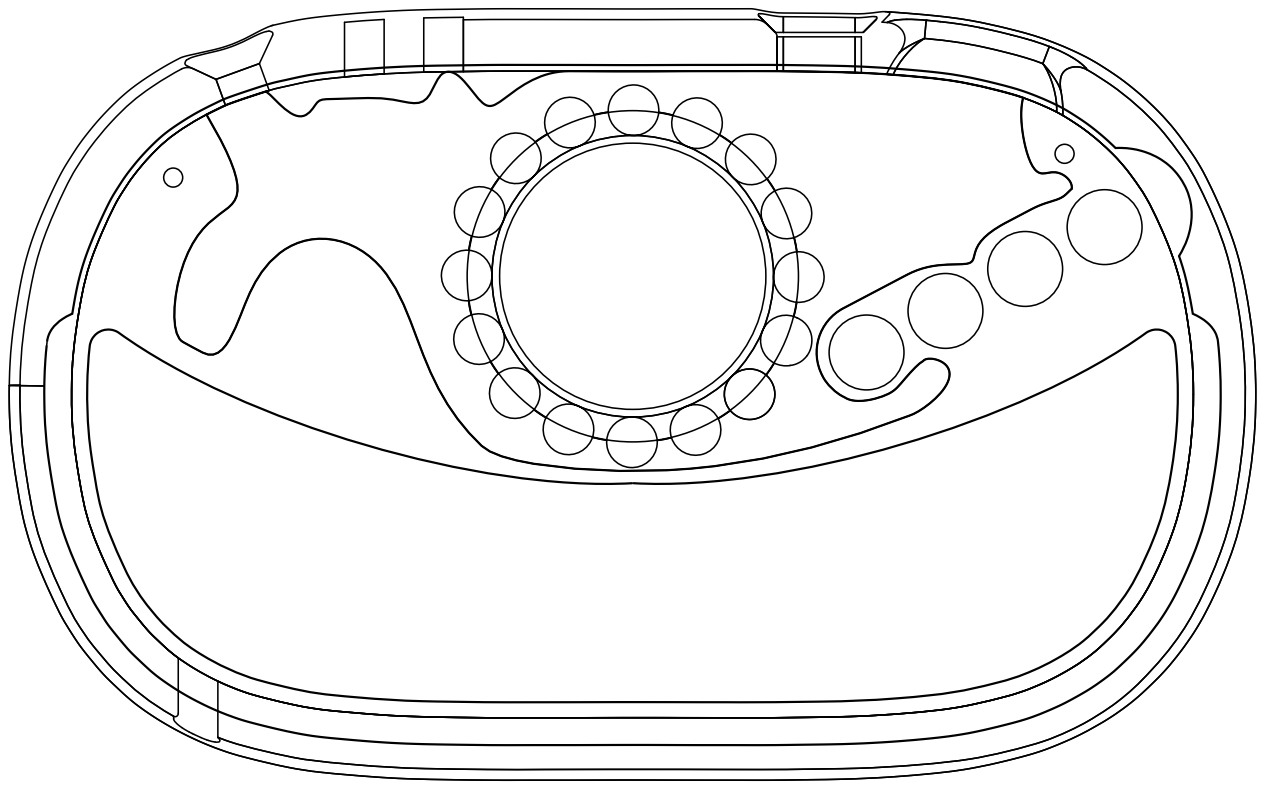
[picture p85: page 1]
