softegg/Stylish-Trucker-Belt-Synthesizer/3d models/woodCNC/Stylish Belt Synth V4 CNC Wood Top Fixture Drawing v0.pdf

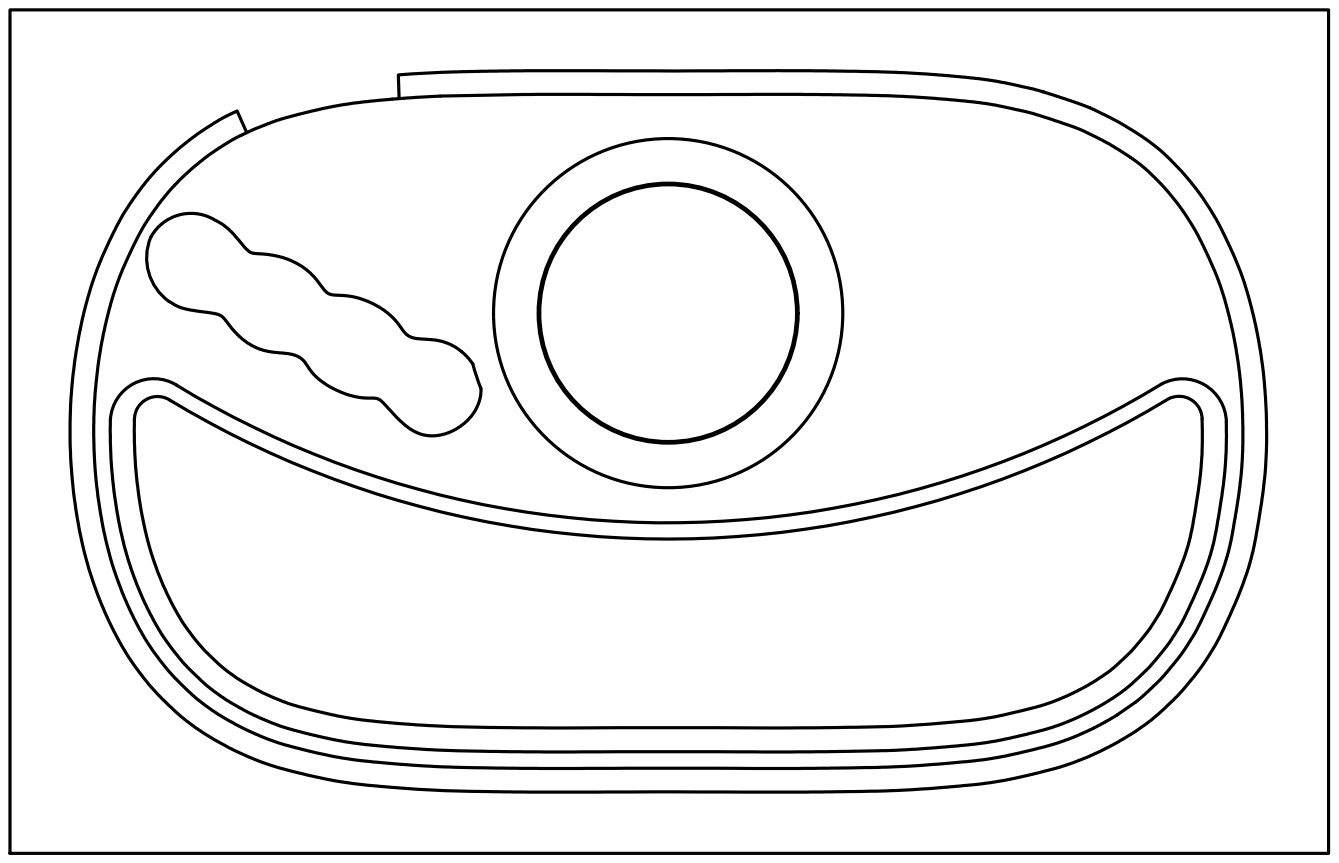
[picture p86: page 1]
