softegg/Stylish-Trucker-Belt-Synthesizer/src/Stylish/cortexm3_macro.h

/******************** (C) COPYRIGHT 2008 STMicroelectronics ********************
* File Name          : cortexm3_macro.h
* Author             : MCD Application Team
* Version            : V2.0.3
* Date               : 09/22/2008
* Description        : Header file for cortexm3_macro.s.
********************************************************************************
* THE PRESENT FIRMWARE WHICH IS FOR GUIDANCE ONLY AIMS AT PROVIDING CUSTOMERS
* WITH CODING INFORMATION REGARDING THEIR PRODUCTS IN ORDER FOR THEM TO SAVE TIME.
* AS A RESULT, STMICROELECTRONICS SHALL NOT BE HELD LIABLE FOR ANY DIRECT,
* INDIRECT OR CONSEQUENTIAL DAMAGES WITH RESPECT TO ANY CLAIMS ARISING FROM THE
* CONTENT OF SUCH FIRMWARE AND/OR THE USE MADE BY CUSTOMERS OF THE CODING
* INFORMATION CONTAINED HEREIN IN CONNECTION WITH THEIR PRODUCTS.
*******************************************************************************/

/* Define to prevent recursive inclusion -------------------------------------*/
#ifndef __CORTEXM3_MACRO_H
#define __CORTEXM3_MACRO_H

/* Includes ------------------------------------------------------------------*/
#include "stm32f10x_type.h"

/* Exported types ------------------------------------------------------------*/
/* Exported constants --------------------------------------------------------*/
/* Exported macro ------------------------------------------------------------*/
/* Exported functions ------------------------------------------------------- */
void __WFI(void);
void __WFE(void);
void __SEV(void);
void __ISB(void);
void __DSB(void);
void __DMB(void);
void __SVC(void);
u32 __MRS_CONTROL(void);
void __MSR_CONTROL(u32 Control);
u32 __MRS_PSP(void);
void __MSR_PSP(u32 TopOfProcessStack);
u32 __MRS_MSP(void);
void __MSR_MSP(u32 TopOfMainStack);
void __RESETPRIMASK(void);
void __SETPRIMASK(void);
u32 __READ_PRIMASK(void);
void __RESETFAULTMASK(void);
void __SETFAULTMASK(void);
u32 __READ_FAULTMASK(void);
void __BASEPRICONFIG(u32 NewPriority);
u32 __GetBASEPRI(void);
u16 __REV_HalfWord(u16 Data);
u32 __REV_Word(u32 Data);

#endif /* __CORTEXM3_MACRO_H */

/******************* (C) COPYRIGHT 2008 STMicroelectronics *****END OF FILE****/
